khu-haeun/MyChip-25y1st-NCO/2_Splited_IO/2_0_Top_NCO/verification/0_rtl_simulation/test_vec/test_for_1000samples.txt

[MODE:0][Sel:Y][FCW:       1][      61]Ref =    -16 vs DUT =    -16 ==> PASS
[MODE:0][Sel:Y][FCW:       1][      68]Ref =    -16 vs DUT =    -16 ==> PASS
[MODE:0][Sel:Y][FCW:       1][      75]Ref =    -16 vs DUT =    -16 ==> PASS
[MODE:0][Sel:Y][FCW:       1][      82]Ref =    -16 vs DUT =    -16 ==> PASS
[MODE:0][Sel:Y][FCW:       1][      89]Ref =    -16 vs DUT =    -16 ==> PASS
[MODE:0][Sel:Y][FCW:       1][      96]Ref =    -16 vs DUT =    -16 ==> PASS
[MODE:0][Sel:Y][FCW:       1][     103]Ref =    -16 vs DUT =    -16 ==> PASS
[MODE:0][Sel:Y][FCW:       1][     110]Ref =    -16 vs DUT =    -16 ==> PASS
[MODE:0][Sel:Y][FCW:       1][     117]Ref =    -16 vs DUT =    -16 ==> PASS
[MODE:0][Sel:Y][FCW:       1][     124]Ref =    -16 vs DUT =    -16 ==> PASS
[MODE:0][Sel:Y][FCW:       1][     131]Ref =    -16 vs DUT =    -16 ==> PASS
[MODE:0][Sel:Y][FCW:       1][     138]Ref =    -16 vs DUT =    -16 ==> PASS
[MODE:0][Sel:Y][FCW:       1][     145]Ref =    -16 vs DUT =    -16 ==> PASS
[MODE:0][Sel:Y][FCW:       1][     152]Ref =    -16 vs DUT =    -16 ==> PASS
[MODE:0][Sel:Y][FCW:       1][     159]Ref =    -16 vs DUT =    -16 ==> PASS
[MODE:0][Sel:Y][FCW:       1][     166]Ref =    -16 vs DUT =    -16 ==> PASS
[MODE:0][Sel:Y][FCW:       1][     173]Ref =    -16 vs DUT =    -16 ==> PASS
[MODE:0][Sel:Y][FCW:       1][     180]Ref =    -16 vs DUT =    -16 ==> PASS
[MODE:0][Sel:Y][FCW:       1][     187]Ref =    -16 vs DUT =    -16 ==> PASS
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
[MODE:0][Sel:Y][FCW:  524288][     173]Ref =     16 vs DUT =     16 ==> PASS
[MODE:0][Sel:Y][FCW:  524288][     180]Ref =    -16 vs DUT =    -16 ==> PASS
[MODE:0][Sel:Y][FCW:  524288][     187]Ref =     16 vs DUT =     16 ==> PASS
[MODE:0][Sel:Y][FCW:  524288][     194]Ref =    -16 vs DUT =    -16 ==> PASS
[MODE:0][Sel:Y][FCW:  524288][     201]Ref =     16 vs DUT =     16 ==> PASS
[MODE:0][Sel:Y][FCW:  524288][     208]Ref =    -16 vs DUT =    -16 ==> PASS
[MODE:0][Sel:Y][FCW:  524288][     215]Ref =     16 vs DUT =     16 ==> PASS
[MODE:0][Sel:Y][FCW:  524288][     222]Ref =    -16 vs DUT =    -16 ==> PASS
[MODE:0][Sel:Y][FCW:  524288][     229]Ref =     16 vs DUT =     16 ==> PASS
[MODE:0][Sel:Y][FCW:  524288][     236]Ref =    -16 vs DUT =    -16 ==> PASS
[MODE:0][Sel:Y][FCW:  524288][     243]Ref =     16 vs DUT =     16 ==> PASS
[MODE:0][Sel:Y][FCW:  524288][     250]Ref =    -16 vs DUT =    -16 ==> PASS
[MODE:0][Sel:Y][FCW:  524288][     257]Ref =     16 vs DUT =     16 ==> PASS
[MODE:0][Sel:Y][FCW:  524288][     264]Ref =    -16 vs DUT =    -16 ==> PASS
[MODE:0][Sel:Y][FCW:  524288][     271]Ref =     16 vs DUT =     16 ==> PASS
[MODE:0][Sel:Y][FCW:  524288][     278]Ref =    -16 vs DUT =    -16 ==> PASS
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
