khu-haeun/MyChip-25y1st-NCO/2_Splited_IO/2_1_Phase_Acc/layout/phase_accumulator.spice

* NGSPICE file created from phase_accumulator.ext - technology: scmos

* Black-box entry subcircuit for FILL abstract view
.subckt FILL vdd gnd
.ends

* Black-box entry subcircuit for OAI21X1 abstract view
.subckt OAI21X1 A B C Y vdd gnd
.ends

* Black-box entry subcircuit for INVX1 abstract view
.subckt INVX1 A Y vdd gnd
.ends

* Black-box entry subcircuit for NAND2X1 abstract view
.subckt NAND2X1 A B Y vdd gnd
.ends

* Black-box entry subcircuit for DFFPOSX1 abstract view
.subckt DFFPOSX1 D CLK Q vdd gnd
.ends

* Black-box entry subcircuit for AOI21X1 abstract view
.subckt AOI21X1 A B C Y vdd gnd
.ends

* Black-box entry subcircuit for AND2X2 abstract view
.subckt AND2X2 A B Y vdd gnd
.ends

* Black-box entry subcircuit for NAND3X1 abstract view
.subckt NAND3X1 A B C Y vdd gnd
.ends

* Black-box entry subcircuit for OR2X2 abstract view
.subckt OR2X2 A B Y vdd gnd
.ends

* Black-box entry subcircuit for NOR2X1 abstract view
.subckt NOR2X1 A B Y vdd gnd
.ends

* Black-box entry subcircuit for BUFX2 abstract view
.subckt BUFX2 A Y vdd gnd
.ends

* Black-box entry subcircuit for AOI22X1 abstract view
.subckt AOI22X1 A B C D Y vdd gnd
.ends

* Black-box entry subcircuit for CLKBUF1 abstract view
.subckt CLKBUF1 A Y vdd gnd
.ends

* Black-box entry subcircuit for INVX2 abstract view
.subckt INVX2 A Y vdd gnd
.ends

* Black-box entry subcircuit for INVX8 abstract view
.subckt INVX8 A Y vdd gnd
.ends

.subckt phase_accumulator gnd vdd Aout[1] Aout[0] En FCW[19] FCW[18] FCW[17] FCW[16]
+ FCW[15] FCW[14] FCW[13] FCW[12] FCW[11] FCW[10] FCW[9] FCW[8] FCW[7] FCW[6] FCW[5]
+ FCW[4] FCW[3] FCW[2] FCW[1] FCW[0] ISout Vld clk
XFILL_5__370_ vdd gnd FILL
XFILL_7__317_ vdd gnd FILL
XFILL_8__581_ vdd gnd FILL
XFILL_2__426_ vdd gnd FILL
XFILL_2__357_ vdd gnd FILL
XFILL_5__568_ vdd gnd FILL
XFILL_5__499_ vdd gnd FILL
X_501_ _501_/A _538_/B _513_/C _502_/B vdd gnd OAI21X1
X_432_ _649_/Q _440_/B _534_/B _433_/C vdd gnd OAI21X1
X_363_ _363_/A _364_/A vdd gnd INVX1
XFILL_6__404_ vdd gnd FILL
XFILL_6__335_ vdd gnd FILL
XFILL_1__375_ vdd gnd FILL
XFILL_1__444_ vdd gnd FILL
XFILL_1__513_ vdd gnd FILL
XFILL_4__586_ vdd gnd FILL
XFILL_5__422_ vdd gnd FILL
XFILL_5__353_ vdd gnd FILL
XFILL_6_CLKBUF1_insert1 vdd gnd FILL
XFILL_8__495_ vdd gnd FILL
XFILL_0__462_ vdd gnd FILL
XFILL_0__600_ vdd gnd FILL
XFILL_0__531_ vdd gnd FILL
XFILL_7_BUFX2_insert7 vdd gnd FILL
XFILL_0__393_ vdd gnd FILL
XFILL_2__409_ vdd gnd FILL
X_415_ _427_/B _427_/A _416_/C vdd gnd NAND2X1
X_346_ _350_/B _346_/B _348_/A vdd gnd NAND2X1
XFILL_4__440_ vdd gnd FILL
XFILL_4__371_ vdd gnd FILL
XFILL_6__318_ vdd gnd FILL
XFILL_7__582_ vdd gnd FILL
XFILL_1__427_ vdd gnd FILL
XFILL_1__358_ vdd gnd FILL
XFILL_4__569_ vdd gnd FILL
XFILL_5__405_ vdd gnd FILL
XFILL_5__336_ vdd gnd FILL
XFILL_8__547_ vdd gnd FILL
XFILL_8__616_ vdd gnd FILL
XFILL_8__478_ vdd gnd FILL
XFILL_0__445_ vdd gnd FILL
XFILL_0__514_ vdd gnd FILL
XFILL_0__376_ vdd gnd FILL
XFILL_3__587_ vdd gnd FILL
X_329_ _329_/A _329_/B _330_/B vdd gnd NAND2X1
XFILL_4__423_ vdd gnd FILL
XFILL_4__354_ vdd gnd FILL
XFILL_7__565_ vdd gnd FILL
XFILL_7__496_ vdd gnd FILL
XFILL74250x39750 vdd gnd FILL
XFILL_8__401_ vdd gnd FILL
XFILL_8__332_ vdd gnd FILL
XFILL_3__510_ vdd gnd FILL
XFILL_3__441_ vdd gnd FILL
XFILL_3__372_ vdd gnd FILL
XFILL_5__319_ vdd gnd FILL
XFILL_6__583_ vdd gnd FILL
XFILL_0__359_ vdd gnd FILL
XFILL_0__428_ vdd gnd FILL
XFILL_7__350_ vdd gnd FILL
XFILL_2__390_ vdd gnd FILL
XFILL_4__406_ vdd gnd FILL
XFILL_4__337_ vdd gnd FILL
XFILL74250x14550 vdd gnd FILL
XFILL74850x18150 vdd gnd FILL
XFILL_7__548_ vdd gnd FILL
XFILL74850x61350 vdd gnd FILL
XFILL_7__617_ vdd gnd FILL
XFILL_7__479_ vdd gnd FILL
XFILL_2__588_ vdd gnd FILL
XFILL_6_BUFX2_insert16 vdd gnd FILL
X_663_ _663_/D _663_/CLK _663_/Q vdd gnd DFFPOSX1
XFILL_3__424_ vdd gnd FILL
X_594_ _594_/A _594_/B _594_/C _638_/D vdd gnd AOI21X1
XFILL_6__566_ vdd gnd FILL
XFILL_3__355_ vdd gnd FILL
XFILL75750x46950 vdd gnd FILL
XFILL_6__497_ vdd gnd FILL
XFILL_7__402_ vdd gnd FILL
XFILL_7__333_ vdd gnd FILL
XFILL_2__511_ vdd gnd FILL
XFILL_2__373_ vdd gnd FILL
XFILL_2__442_ vdd gnd FILL
XFILL_5__584_ vdd gnd FILL
XFILL_6__420_ vdd gnd FILL
XFILL_6__351_ vdd gnd FILL
XFILL_3__407_ vdd gnd FILL
XFILL_1__391_ vdd gnd FILL
X_646_ _646_/D _664_/CLK _646_/Q vdd gnd DFFPOSX1
XFILL_1__460_ vdd gnd FILL
X_577_ _637_/Q FCW[4] _625_/B vdd gnd AND2X2
XFILL75750x21750 vdd gnd FILL
XFILL_6__549_ vdd gnd FILL
XFILL_3__338_ vdd gnd FILL
XFILL_6__618_ vdd gnd FILL
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
XFILL_4__543_ vdd gnd FILL
X_449_ _465_/B _465_/A _454_/A vdd gnd NAND2X1
XFILL_1__332_ vdd gnd FILL
XFILL_4__612_ vdd gnd FILL
XFILL_4__474_ vdd gnd FILL
XFILL_1_BUFX2_insert13 vdd gnd FILL
XFILL_8__521_ vdd gnd FILL
XFILL_8__383_ vdd gnd FILL
XFILL_8__452_ vdd gnd FILL
XFILL_0__350_ vdd gnd FILL
XFILL_3__561_ vdd gnd FILL
XFILL_3__492_ vdd gnd FILL
XFILL_5__508_ vdd gnd FILL
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
