khu-haeun/MyChip-25y1st-NCO/2_Splited_IO/2_3_Output_Terminal/layout/output_terminal.spice

* NGSPICE file created from output_terminal.ext - technology: scmos

* Black-box entry subcircuit for FILL abstract view
.subckt FILL vdd gnd
.ends

* Black-box entry subcircuit for NAND3X1 abstract view
.subckt NAND3X1 A B C Y vdd gnd
.ends

* Black-box entry subcircuit for NAND2X1 abstract view
.subckt NAND2X1 A B Y vdd gnd
.ends

* Black-box entry subcircuit for INVX1 abstract view
.subckt INVX1 A Y vdd gnd
.ends

* Black-box entry subcircuit for NOR2X1 abstract view
.subckt NOR2X1 A B Y vdd gnd
.ends

* Black-box entry subcircuit for OAI21X1 abstract view
.subckt OAI21X1 A B C Y vdd gnd
.ends

* Black-box entry subcircuit for DFFPOSX1 abstract view
.subckt DFFPOSX1 D CLK Q vdd gnd
.ends

* Black-box entry subcircuit for AND2X2 abstract view
.subckt AND2X2 A B Y vdd gnd
.ends

* Black-box entry subcircuit for OR2X2 abstract view
.subckt OR2X2 A B Y vdd gnd
.ends

* Black-box entry subcircuit for BUFX2 abstract view
.subckt BUFX2 A Y vdd gnd
.ends

* Black-box entry subcircuit for AOI22X1 abstract view
.subckt AOI22X1 A B C D Y vdd gnd
.ends

* Black-box entry subcircuit for INVX2 abstract view
.subckt INVX2 A Y vdd gnd
.ends

* Black-box entry subcircuit for INVX8 abstract view
.subckt INVX8 A Y vdd gnd
.ends

* Black-box entry subcircuit for CLKBUF1 abstract view
.subckt CLKBUF1 A Y vdd gnd
.ends

* Black-box entry subcircuit for AOI21X1 abstract view
.subckt AOI21X1 A B C Y vdd gnd
.ends

* Black-box entry subcircuit for INVX4 abstract view
.subckt INVX4 A Y vdd gnd
.ends

.subckt output_terminal gnd vdd Dout[11] Dout[10] Dout[9] Dout[8] Dout[7] Dout[6]
+ Dout[5] Dout[4] Dout[3] Dout[2] Dout[1] Dout[0] ISin Rdy Vld Xin[1] Xin[0] Yin[1]
+ Yin[0] clk selSign selXY
XFILL_5__370_ vdd gnd FILL
XFILL_7__317_ vdd gnd FILL
XFILL_2__288_ vdd gnd FILL
XFILL_2__426_ vdd gnd FILL
XFILL_2__357_ vdd gnd FILL
X_501_ _625_/A _501_/B _501_/C _502_/C vdd gnd NAND3X1
XFILL_5__499_ vdd gnd FILL
X_432_ _432_/A _432_/B _433_/B vdd gnd NAND2X1
X_294_ _577_/Q _479_/A vdd gnd INVX1
X_363_ _590_/Q _591_/Q _367_/B vdd gnd NOR2X1
XFILL_9__615_ vdd gnd FILL
XFILL_6__404_ vdd gnd FILL
XFILL_0_CLKBUF1_insert6 vdd gnd FILL
XFILL_6__335_ vdd gnd FILL
XFILL_9__477_ vdd gnd FILL
XFILL_9__546_ vdd gnd FILL
XFILL_1__513_ vdd gnd FILL
XFILL_1__444_ vdd gnd FILL
XFILL_1__375_ vdd gnd FILL
XFILL_5__422_ vdd gnd FILL
XFILL_5__353_ vdd gnd FILL
XFILL_8__495_ vdd gnd FILL
XFILL_5__284_ vdd gnd FILL
XFILL_6_CLKBUF1_insert1 vdd gnd FILL
XFILL_0__462_ vdd gnd FILL
XFILL_7_BUFX2_insert7 vdd gnd FILL
XFILL_0__531_ vdd gnd FILL
XFILL_2__409_ vdd gnd FILL
XFILL_0__393_ vdd gnd FILL
XFILL_9__331_ vdd gnd FILL
X_415_ _415_/A _582_/Q _417_/B _419_/B vdd gnd NAND3X1
X_346_ _346_/A _346_/B _348_/B vdd gnd NAND2X1
X_277_ _286_/A _559_/Q _278_/C vdd gnd NAND2X1
XFILL_4__440_ vdd gnd FILL
XFILL_6__318_ vdd gnd FILL
XFILL_4__371_ vdd gnd FILL
XFILL_9__529_ vdd gnd FILL
XFILL_1__427_ vdd gnd FILL
XFILL_1__358_ vdd gnd FILL
XFILL_1__289_ vdd gnd FILL
XFILL_8__280_ vdd gnd FILL
XFILL_5__336_ vdd gnd FILL
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
XFILL_9__503_ vdd gnd FILL
XFILL_0__496_ vdd gnd FILL
XFILL_9__296_ vdd gnd FILL
XBUFX2_insert9 selXY _305_/A vdd gnd BUFX2
X_518_ _612_/D _525_/B _519_/B vdd gnd NAND2X1
XFILL_9__365_ vdd gnd FILL
XFILL_1__401_ vdd gnd FILL
X_449_ _603_/Q _450_/A _451_/B vdd gnd NAND2X1
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
