khu-haeun/MyChip-25y1st-NCO/2_Splited_IO/2_0_Top_NCO/source/netlist/asic/output_terminal.v

/* Verilog module written by vlog2Verilog (qflow) */

module output_terminal(
    output [11:0] Dout,
    input ISin,
    input Rdy,
    output Vld,
    input [1:0] Xin,
    input [1:0] Yin,
    input clk,
    input selSign,
    input selXY
);
/* verilator coverage_off */
wire vdd = 1'b1;
wire gnd = 1'b0;
/* verilator coverage_on */

wire _168_ ;
wire _60_ ;
wire _19_ ;
wire [6:0] LoadCtl ;
wire _57_ ;
wire _130_ ;
wire _95_ ;
wire _224_ ;
wire _262_ ;
wire _127_ ;
wire _165_ ;
wire _259_ ;
wire _16_ ;
wire _54_ ;
wire _92_ ;
wire _221_ ;
//wire ISin ;
wire _124_ ;
wire _89_ ;
wire _162_ ;
wire _218_ ;
wire _256_ ;
wire _13_ ;
wire _159_ ;
wire _51_ ;
//wire Rdy ;
wire _197_ ;
wire _7_ ;
wire _48_ ;
wire _121_ ;
wire _86_ ;
wire _215_ ;
wire _253_ ;
wire _118_ ;
wire _10_ ;
wire _156_ ;
wire _194_ ;
wire _4_ ;
wire _45_ ;
wire _83_ ;
wire _212_ ;
wire _250_ ;
wire _115_ ;
wire _153_ ;
wire _209_ ;
wire _191_ ;
wire _247_ ;
wire clk_bF$buf0 ;
wire clk_bF$buf1 ;
wire clk_bF$buf2 ;
wire clk_bF$buf3 ;
wire clk_bF$buf4 ;
wire clk_bF$buf5 ;
wire clk_bF$buf6 ;
wire _1_ ;
wire _42_ ;
wire _188_ ;
wire ISreg_bF$buf0 ;
wire ISreg_bF$buf1 ;
wire ISreg_bF$buf2 ;
wire ISreg_bF$buf3 ;
wire ISreg_bF$buf4 ;
wire _80_ ;
wire _39_ ;
wire _112_ ;
//wire clk ;
wire _77_ ;
wire _150_ ;
wire _206_ ;
wire _244_ ;
wire _109_ ;
wire selXY_bF$buf0 ;
wire selXY_bF$buf1 ;
wire selXY_bF$buf2 ;
wire selXY_bF$buf3 ;
wire _147_ ;
wire _185_ ;
//wire selXY ;
//wire selSign ;
wire _36_ ;
wire _74_ ;
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
    .Y(Dout[5])
);

BUFX2 _621_ (
    .A(_272_[6]),
    .Y(Dout[6])
);

BUFX2 _622_ (
    .A(_272_[7]),
    .Y(Dout[7])
);

BUFX2 _623_ (
    .A(_272_[8]),
    .Y(Dout[8])
);

BUFX2 _624_ (
    .A(_272_[9]),
    .Y(Dout[9])
);

BUFX2 _625_ (
    .A(LoadCtl_6_bF$buf4),
    .Y(Vld)
);

endmodule
