khu-haeun/MyChip-25y1st-NCO/2_Splited_IO/2_1_Phase_Acc/synthesis/phase_accumulator.rtl.v

/* Verilog module written by vlog2Verilog (qflow) */
/* With explicit power connections */

module phase_accumulator(
    inout vdd,
    inout gnd,
    output [1:0] Aout,
    input En,
    input [19:0] FCW,
    output ISout,
    output Vld,
    input clk
);

wire _168_ ;
wire _60_ ;
wire _19_ ;
wire _57_ ;
wire _130_ ;
wire _95_ ;
wire _224_ ;
wire _262_ ;
wire _127_ ;
wire _165_ ;
wire _259_ ;
wire _297_ ;
wire _16_ ;
wire _54_ ;
wire _92_ ;
wire _221_ ;
wire _124_ ;
wire _89_ ;
wire _162_ ;
wire _73__bF$buf0 ;
wire _73__bF$buf1 ;
wire _73__bF$buf2 ;
wire _73__bF$buf3 ;
wire _73__bF$buf4 ;
wire _218_ ;
wire _256_ ;
wire _294_ ;
wire _13_ ;
wire _159_ ;
wire _51_ ;
wire _197_ ;
wire _7_ ;
wire _312_ ;
wire _48_ ;
wire _121_ ;
wire ISout ;
wire _86_ ;
wire _215_ ;
wire _253_ ;
wire [11:0] Atmp ;
wire _309_ ;
wire _118_ ;
wire _291_ ;
wire _10_ ;
wire _156_ ;
wire _194_ ;
wire _288_ ;
wire _4_ ;
wire _45_ ;
wire _83_ ;
wire [19:0] acc_reg ;
wire _212_ ;
wire _250_ ;
wire _306_ ;
wire En_bF$buf0 ;
wire En_bF$buf1 ;
wire En_bF$buf2 ;
wire En_bF$buf3 ;
wire En_bF$buf4 ;
wire _115_ ;
wire _153_ ;
wire _209_ ;
wire _191_ ;
wire _247_ ;
wire clk_bF$buf0 ;
wire clk_bF$buf1 ;
wire clk_bF$buf2 ;
wire clk_bF$buf3 ;
wire clk_bF$buf4 ;
wire clk_bF$buf5 ;
wire _285_ ;
wire _1_ ;
wire _42_ ;
wire _188_ ;
wire _80_ ;
wire _303_ ;
wire _39_ ;
wire _112_ ;
wire clk ;
wire _77_ ;
wire _150_ ;
wire _206_ ;
wire _244_ ;
wire _109_ ;
wire _282_ ;
wire _147_ ;
wire _185_ ;
wire _279_ ;
wire _300_ ;
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
    .vdd(vdd)
);

FILL FILL_3_BUFX2_insert20 (
    .gnd(gnd),
    .vdd(vdd)
);

FILL FILL_5__372_ (
    .gnd(gnd),
    .vdd(vdd)
);

FILL FILL_6__314_ (
    .gnd(gnd),
    .vdd(vdd)
);

FILL FILL_7__521_ (
    .gnd(gnd),
    .vdd(vdd)
);

FILL FILL_0__463_ (
    .gnd(gnd),
    .vdd(vdd)
);
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
