khu-haeun/MyChip-25y1st-NCO/2_Splited_IO/2_1_Phase_Acc/synthesis/phase_accumulator.rtlbb.v

/* Verilog module written by vlog2Verilog (qflow) */
/* With bit-blasted vectors */
/* With power connections converted to binary 1, 0 */

module phase_accumulator(
    output [1:0] Aout,
    input En,
    input [19:0] FCW,
    output ISout,
    output Vld,
    input clk
);

wire _168_ ;
wire _60_ ;
wire _19_ ;
wire _57_ ;
wire _130_ ;
wire _95_ ;
wire _224_ ;
wire _262_ ;
wire _127_ ;
wire _165_ ;
wire _259_ ;
wire _297_ ;
wire _16_ ;
wire _54_ ;
wire _92_ ;
wire _221_ ;
wire _124_ ;
wire _89_ ;
wire _162_ ;
wire _73__bF$buf0 ;
wire _73__bF$buf1 ;
wire _73__bF$buf2 ;
wire _73__bF$buf3 ;
wire _73__bF$buf4 ;
wire _218_ ;
wire _256_ ;
wire _294_ ;
wire _13_ ;
wire _159_ ;
wire _51_ ;
wire _197_ ;
wire _7_ ;
wire _312_ ;
wire _48_ ;
wire _121_ ;
wire ISout ;
wire _86_ ;
wire _215_ ;
wire _253_ ;
wire [11:0] Atmp ;
wire _309_ ;
wire _118_ ;
wire _291_ ;
wire _10_ ;
wire _156_ ;
wire _194_ ;
wire _288_ ;
wire _4_ ;
wire _45_ ;
wire _83_ ;
wire [19:0] acc_reg ;
wire _212_ ;
wire _250_ ;
wire _306_ ;
wire En_bF$buf0 ;
wire En_bF$buf1 ;
wire En_bF$buf2 ;
wire En_bF$buf3 ;
wire En_bF$buf4 ;
wire _115_ ;
wire _153_ ;
wire _209_ ;
wire _191_ ;
wire _247_ ;
wire clk_bF$buf0 ;
wire clk_bF$buf1 ;
wire clk_bF$buf2 ;
wire clk_bF$buf3 ;
wire clk_bF$buf4 ;
wire clk_bF$buf5 ;
wire _285_ ;
wire _1_ ;
wire _42_ ;
wire _188_ ;
wire _80_ ;
wire _303_ ;
wire _39_ ;
wire _112_ ;
wire clk ;
wire _77_ ;
wire _150_ ;
wire _206_ ;
wire _244_ ;
wire _109_ ;
wire _282_ ;
wire _147_ ;
wire _185_ ;
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

FILL FILL_3__368_ (
);

DFFPOSX1 _647_ (
    .D(_21_),
    .CLK(clk_bF$buf0),
    .Q(acc_reg[14])
);

FILL FILL74850x36150 (
);

FILL FILL_1__431_ (
);

FILL FILL_4__575_ (
);

FILL FILL_5__609_ (
);

FILL FILL_5__362_ (
);

FILL FILL_7__511_ (
);

FILL FILL_0__453_ (
);

FILL FILL_3__597_ (
);

AOI21X1 _456_ (
    .A(_284_),
    .B(RdyCtl_6_bF$buf2),
    .C(_285_),
    .Y(_25_)
);

FILL FILL_4__384_ (
);

FILL FILL_5__418_ (
);

FILL FILL_5__591_ (
);

FILL FILL_6__533_ (
);

FILL FILL_0__509_ (
);

FILL FILL_7__320_ (
);

FILL FILL_2__503_ (
);

FILL FILL_6__342_ (
);

FILL FILL_0__318_ (
);

FILL FILL_0__491_ (
);

FILL FILL_1__525_ (
);

INVX1 _494_ (
    .A(Atmp[4]),
    .Y(_39_)
);

FILL FILL_5__456_ (
);

FILL FILL_6__571_ (
);

FILL FILL_7__605_ (
);

FILL FILL_0__547_ (
);

FILL FILL_1__334_ (
);

FILL FILL_4__478_ (
);

FILL FILL_2__541_ (
);

FILL FILL_6__380_ (
);

FILL FILL_7__414_ (
);

FILL FILL_0__356_ (
);

NAND2X1 _359_ (
    .A(acc_reg[12]),
    .B(_73__bF$buf4),
    .Y(_195_)
);

FILL FILL_1__563_ (
);

endmodule
