khu-haeun/MyChip-25y1st-NCO/2_Splited_IO/2_2_Cordic_Element/synthesis/cordic_element.rtl.v

/* Verilog module written by vlog2Verilog (qflow) */
/* With explicit power connections */

module cordic_element(
    inout vdd,
    inout gnd,
    input [1:0] Ain,
    output [1:0] Aout,
    input ISin,
    output ISout,
    input Rdy,
    input [2:0] Stg,
    output Vld,
    input [1:0] Xin,
    output [1:0] Xout,
    input [1:0] Yin,
    output [1:0] Yout,
    input clk
);

wire _588_ ;
wire _168_ ;
wire _800_ ;
wire _60_ ;
wire _397_ ;
wire _703_ ;
wire _19_ ;
wire _512_ ;
wire [6:0] LoadCtl ;
wire _741_ ;
wire _321_ ;
wire _57_ ;
wire _550_ ;
wire _130_ ;
wire _606_ ;
wire _835_ ;
wire _415_ ;
wire _95_ ;
wire _644_ ;
wire _224_ ;
wire _453_ ;
wire _509_ ;
wire _682_ ;
wire _262_ ;
wire _738_ ;
wire _318_ ;
wire _491_ ;
wire _547_ ;
wire _127_ ;
wire _776_ ;
wire _356_ ;
wire _585_ ;
wire _165_ ;
wire _394_ ;
wire _679_ ;
wire _259_ ;
wire _488_ ;
wire _700_ ;
wire _297_ ;
wire _16_ ;
wire _54_ ;
wire _603_ ;
wire _832_ ;
wire _412_ ;
wire _92_ ;
wire _641_ ;
wire _221_ ;
wire _450_ ;
wire ISin ;
wire _506_ ;
wire [11:0] Acalc ;
wire _735_ ;
wire _315_ ;
wire _544_ ;
wire _124_ ;
wire _773_ ;
wire _353_ ;
wire _829_ ;
wire _409_ ;
wire _89_ ;
wire _582_ ;
wire _162_ ;
wire _638_ ;
wire _218_ ;
wire _391_ ;
wire _447_ ;
wire _676_ ;
wire _256_ ;
wire _485_ ;
wire _294_ ;
wire _13_ ;
wire _579_ ;
wire _159_ ;
wire _51_ ;
wire _388_ ;
wire _600_ ;
wire Rdy ;
wire _197_ ;
wire _7_ ;
wire _503_ ;
wire _732_ ;
wire _312_ ;
wire _48_ ;
wire _541_ ;
wire _121_ ;
wire ISout ;
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
    .gnd(gnd),
    .vdd(vdd)
);

AOI21X1 _996_ (
    .gnd(gnd),
    .vdd(vdd),
    .A(_231_),
    .B(_230_),
    .C(_192_),
    .Y(_232_)
);

FILL FILL_0__1705_ (
    .gnd(gnd),
    .vdd(vdd)
);

NAND2X1 _1474_ (
    .gnd(gnd),
    .vdd(vdd),
    .A(Ain[1]),
    .B(_629_),
    .Y(_658_)
);
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
